NeDaMo93/Wearable_ECG_ADS1293_nrf52840/Wearable_ECG_ADS1293_nrf52840/src/bluetooth_connection.c

#include "bluetooth_connection.h"
#include <zephyr/kernel.h>
#include <zephyr/device.h>
#include <bluetooth/services/lbs.h>
#include <zephyr/settings/settings.h>
#include <dk_buttons_and_leds.h>
#include <zephyr/types.h>
#include <stddef.h>
#include <string.h>
#include <errno.h>
#include <zephyr/sys/printk.h>
#include <zephyr/sys/byteorder.h>
#include <zephyr/kernel.h>
#include <zephyr/drivers/gpio.h>
#include <soc.h>

#include <zephyr/bluetooth/bluetooth.h>
#include <zephyr/bluetooth/hci.h>
#include <zephyr/bluetooth/conn.h>
#include <zephyr/bluetooth/uuid.h>
#include <zephyr/bluetooth/gatt.h>
#include <zephyr/drivers/sensor.h>
#include <math.h>
#include <stdio.h>
#include <stdbool.h>

#define RUN_STATUS_LED          		DK_LED1
#define DEVICE_NAME             CONFIG_BT_DEVICE_NAME
#define DEVICE_NAME_LEN         (sizeof(DEVICE_NAME) - 1)
static bool app_led_state = false;
static bool app_button_state;

#if defined(CONFIG_BT_LBS_SECURITY_ENABLED)
static void auth_passkey_display(struct bt_conn *conn, unsigned int passkey)
{
	char addr[BT_ADDR_LE_STR_LEN];

	bt_addr_le_to_str(bt_conn_get_dst(conn), addr, sizeof(addr));

	printk("Passkey for %s: %06u\n", addr, passkey);
}
static void auth_cancel(struct bt_conn *conn)
{
	char addr[BT_ADDR_LE_STR_LEN];

	bt_addr_le_to_str(bt_conn_get_dst(conn), addr, sizeof(addr));

	printk("Pairing cancelled: %s\n", addr);
}

void app_led_cb(bool led_state)
{
    if (app_led_state != led_state)
    {
        app_led_state = led_state;
        dk_set_led(RUN_STATUS_LED, app_led_state);
    }
}

static void pairing_failed(struct bt_conn *conn, enum bt_security_err reason)
{
	char addr[BT_ADDR_LE_STR_LEN];

	bt_addr_le_to_str(bt_conn_get_dst(conn), addr, sizeof(addr));

	printk("Pairing failed conn: %s, reason %d\n", addr, reason);
}

static void pairing_complete(struct bt_conn *conn, bool bonded)
{
	char addr[BT_ADDR_LE_STR_LEN];

	bt_addr_le_to_str(bt_conn_get_dst(conn), addr, sizeof(addr));

	printk("Pairing completed: %s, bonded: %d\n", addr, bonded);
}

static bool app_button_cb(void)
{
	return app_button_state;
}

static const struct bt_data sd[] = {
	BT_DATA_BYTES(BT_DATA_UUID128_ALL, BT_UUID_LBS_VAL),
};

static const struct bt_data ad[] = {
	BT_DATA_BYTES(BT_DATA_FLAGS, (BT_LE_AD_GENERAL | BT_LE_AD_NO_BREDR)),
	BT_DATA(BT_DATA_NAME_COMPLETE, DEVICE_NAME, DEVICE_NAME_LEN),
};
static struct bt_lbs_cb lbs_callbacs = {
	.led_cb    = app_led_cb,
	.button_cb = app_button_cb,
};

static struct bt_conn_auth_cb conn_auth_callbacks = {
	.passkey_display = auth_passkey_display,
	.cancel = auth_cancel,
};
static struct bt_conn_auth_info_cb conn_auth_info_callbacks = {
	.pairing_complete = pairing_complete,
	.pairing_failed = pairing_failed
};
#else
static struct bt_conn_auth_cb conn_auth_callbacks;
static struct bt_conn_auth_info_cb conn_auth_info_callbacks;
#endif


void Bluetooth_init(void)
{
	int err;
	printk("Starting Bluetooth Peripheral LBS example\n");
	err = dk_leds_init();
	if (err) {
		printk("LEDs init failed (err %d)\n", err);
		return;
	}

	if (IS_ENABLED(CONFIG_BT_LBS_SECURITY_ENABLED)) {
		err = bt_conn_auth_cb_register(&conn_auth_callbacks);
		if (err) {
			printk("Failed to register authorization callbacks.\n");
			return;
		}

		err = bt_conn_auth_info_cb_register(&conn_auth_info_callbacks);
		if (err) {
			printk("Failed to register authorization info callbacks.\n");
			return;
		}
	}

	err = bt_enable(NULL);
	if (err) {
		printk("Bluetooth init failed (err %d)\n", err);
		return;
	}

	printk("Bluetooth initialized\n");

	if (IS_ENABLED(CONFIG_SETTINGS)) {
		settings_load();
	}

	err = bt_lbs_init(&lbs_callbacs);
	if (err) {
		printk("Failed to init LBS (err:%d)\n", err);
		return;
	}

	err = bt_le_adv_start(BT_LE_ADV_CONN, ad, ARRAY_SIZE(ad),
			      sd, ARRAY_SIZE(sd));
	if (err) {
		printk("Advertising failed to start (err %d)\n", err);
		return;
	}

	printk("Advertising successfully started\n");
}
