NeDaMo93/Wearable_ECG_ADS1293_nrf52840/lbs.h

/*
 * Copyright (c) 2018 Nordic Semiconductor ASA
 *
 * SPDX-License-Identifier: LicenseRef-Nordic-5-Clause
 */

#ifndef BT_LBS_H_
#define BT_LBS_H_

/**@file
 * @defgroup bt_lbs LED Button Service API
 * @{
 * @brief API for the LED Button Service (LBS).
 */

#ifdef __cplusplus
extern "C" {
#endif

#include <zephyr/types.h>

/** @brief LBS Service UUID. */
#define BT_UUID_LBS_VAL \
	BT_UUID_128_ENCODE(0x00001523, 0x1212, 0xefde, 0x1523, 0x785feabcd123)

/** @brief Button Characteristic UUID. */
#define BT_UUID_ECG_DATA_VAL \
	BT_UUID_128_ENCODE(0x00001524, 0x1212, 0xefde, 0x1523, 0x785feabcd123)

/** @brief Temp_IMU Characteristic UUID. */
#define Temp_IMU_UUID_VAL \
	BT_UUID_128_ENCODE(0x00001525, 0x1212, 0xefde, 0x1523, 0x785feabcd123)
/** @brief Temp_Body_Position Characteristic UUID. */
#define Temp_BODY_POSITION_UUID_VAL \
	BT_UUID_128_ENCODE(0x00001526, 0x1212, 0xefde, 0x1523, 0x785feabcd123)


#define BT_UUID_LBS           			BT_UUID_DECLARE_128(BT_UUID_LBS_VAL)
#define BT_UUID_ECG_DATA      			BT_UUID_DECLARE_128(BT_UUID_ECG_DATA_VAL)
#define Temp_IMU_UUID         			BT_UUID_DECLARE_128(Temp_IMU_UUID_VAL)
#define Temp_BODY_POSITION_UUID         BT_UUID_DECLARE_128(Temp_BODY_POSITION_UUID_VAL)

/** @brief Callback type for when an LED state change is received. */
typedef void (*led_cb_t)(const bool led_state);

/** @brief Callback type for when the button state is pulled. */
typedef bool (*button_cb_t)(void);
typedef bool (*temp_IMU_t)(void);

/** @brief Callback struct used by the LBS Service. */
struct bt_lbs_cb {
	/** LED state change callback. */
	led_cb_t    led_cb;
	/** ECG Data read callback. */
	button_cb_t button_cb;
	/** Tem IMU read callback. */
	temp_IMU_t temp_imu_cb;
};

/** @brief Initialize the LBS Service.
 *
 * This function registers a GATT service with two characteristics: Button
 * and LED.
 * Send notifications for the Button Characteristic to let connected peers know
 * when the button state changes.
 * Write to the LED Characteristic to change the state of the LED on the
 * board.
 *
 * @param[in] callbacks Struct containing pointers to callback functions
 *			used by the service. This pointer can be NULL
 *			if no callback functions are defined.
 *
 *
 * @retval 0 If the operation was successful.
 *           Otherwise, a (negative) error code is returned.
 */
int bt_lbs_init(struct bt_lbs_cb *callbacks);

/** @brief Send the button state.
 *
 * This function sends a binary state, typically the state of a
 * button, to all connected peers.
 *
 * @param[in] button_state The state of the button.
 *
 * @retval 0 If the operation was successful.
 *           Otherwise, a (negative) error code is returned.
 */
int bt_lbs_send_button_state(bool button_state);
int send_ECG_Packet_Data(uint32_t *ecg_data_val, size_t buf_size);
int send_temp_IMU_Packet_Data(uint32_t *mag_acc_vec, size_t buf_size);
struct bt_gatt_service *get_lbs_service(void);
bool get_notify_enabled(void);
bool get_notify_enabled(void);

#ifdef __cplusplus
}
#endif

/**
 * @}
 */

#endif /* BT_LBS_H_ */
