NeDaMo93/Wearable_ECG_ADS1293_nrf52840/Wearable_ECG_ADS1293_nrf52840/src/bluetooth_connection.h

#ifndef BLUETOOTH_CONNECTION_H
#define BLUETOOTH_CONNECTION_H

#include <zephyr/kernel.h>
#include <dk_buttons_and_leds.h>
#include <zephyr/bluetooth/bluetooth.h>
#include <bluetooth/services/lbs.h>

void Bluetooth_init(void);

#endif // BLUETOOTH_CONNECTION_H
