NeDaMo93/Wearable_ECG_ADS1293_nrf52840/Wearable_ECG_ADS1293_nrf52840/src/connexion_check.c

#include "connexion_check.h"
#include <zephyr/bluetooth/bluetooth.h>
#include <zephyr/bluetooth/hci.h>
#include <zephyr/bluetooth/conn.h>
#include <zephyr/bluetooth/uuid.h>
#include <zephyr/bluetooth/gatt.h>

#include <bluetooth/services/lbs.h>

#include <zephyr/logging/log.h>
#include <math.h> 
#include <stdio.h>

#define CON_STATUS_LED                
#ifdef CONFIG_BT_LBS_SECURITY_ENABLED

static void security_changed(struct bt_conn *conn, bt_security_t level,
			     enum bt_security_err err)
{
	char addr[BT_ADDR_LE_STR_LEN];

	bt_addr_le_to_str(bt_conn_get_dst(conn), addr, sizeof(addr));

	if (!err) {
		printk("Security changed: %s level %u\n", addr, level);
	} else {
		printk("Security failed: %s level %u err %d\n", addr, level,
			err);
	}
}
#endif

BT_CONN_CB_DEFINE(conn_callbacks) = {
	.connected        = connected,
	.disconnected     = disconnected,
#ifdef CONFIG_BT_LBS_SECURITY_ENABLED
	.security_changed = security_changed,
#endif
};

void connected(struct bt_conn *conn, uint8_t err)
{
	if (err) {
		printk("Connection failed (err %u)\n", err);
		return;
	}

	printk("Connected\n");

	dk_set_led_on(CON_STATUS_LED);
}

void disconnected(struct bt_conn *conn, uint8_t reason)
{
	printk("Disconnected (reason %u)\n", reason);

	dk_set_led_off(CON_STATUS_LED);
}
